drewsum/audio_visualiser/hdw/project_lib/3d_models/Abracon_ASE_3.2x2.5mm.step

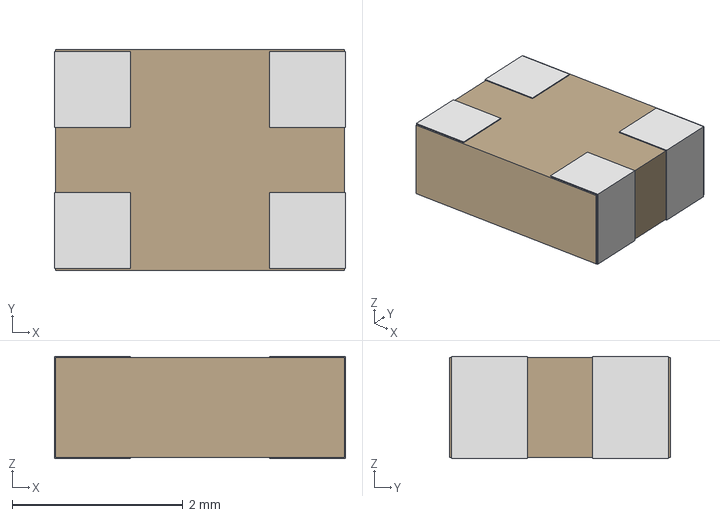
[picture p20: CAD file, 2026-10-09]
hdw/project_lib/3d_models/Abracon_ASE_3.2x2.5mm.step
3.40 x 2.59 x 1.19 mm
