drewsum/audio_visualiser/hdw/project_lib/3d_models/TI_TPS259474_RPW0010A.step

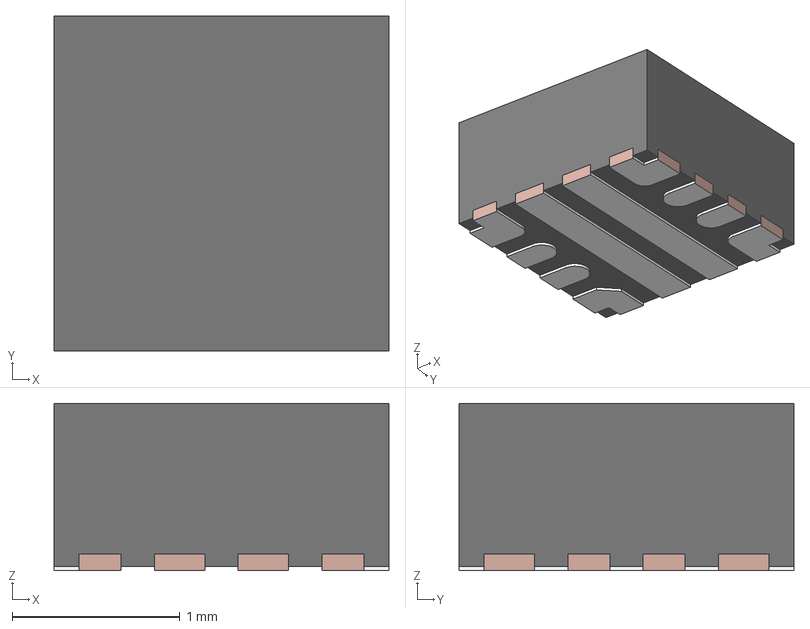
[picture p21: CAD file, 2026-10-09]
hdw/project_lib/3d_models/TI_TPS259474_RPW0010A.step
2.00 x 2.00 x 1.00 mm
FRAME
MOLD
