drewsum/audio_visualiser/hdw/project_lib/3d_models/JAE_DX07S016JA1R1500.step

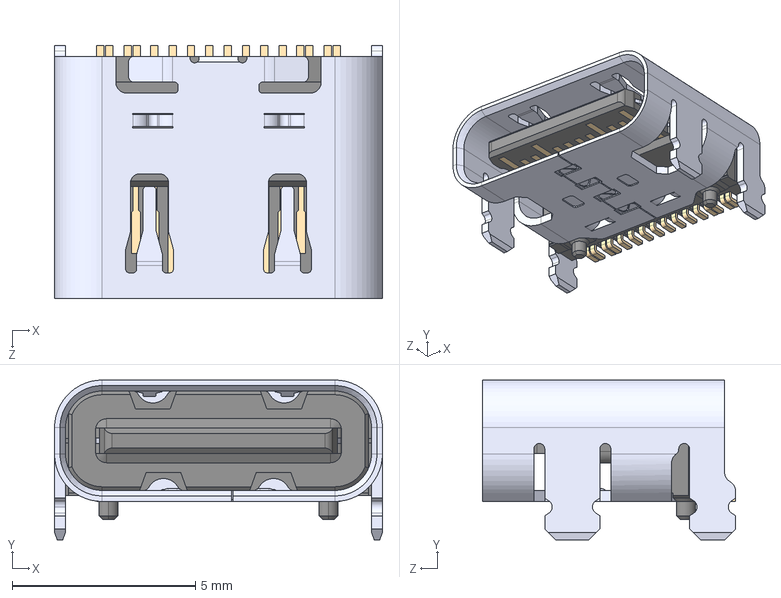
[picture p22: CAD file, 2026-10-09]
hdw/project_lib/3d_models/JAE_DX07S016JA1R1500.step
8.94 x 4.36 x 6.90 mm
