drewsum/audio_visualiser/hdw/project_lib/3d_models/Qorvo_TQFN66-48-1EP_6x6mm_P0.4mm_EP4.2x4.2mm.step

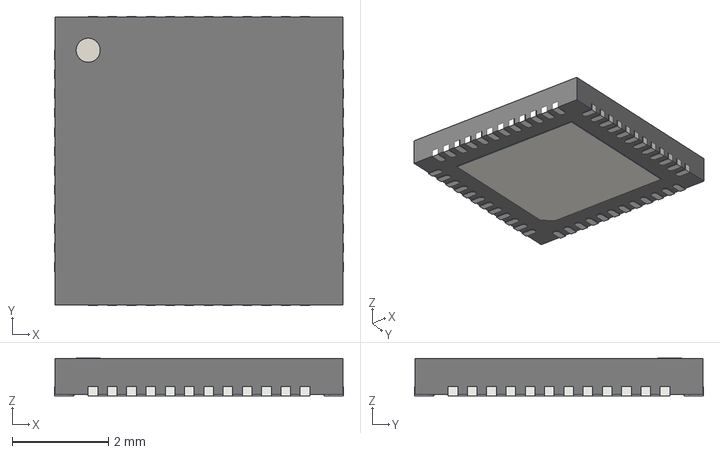
[picture p23: CAD file, 2026-10-09]
hdw/project_lib/3d_models/Qorvo_TQFN66-48-1EP_6x6mm_P0.4mm_EP4.2x4.2mm.step
6.00 x 6.00 x 0.785 mm
