drewsum/audio_visualiser/hdw/project_lib/3d_models/R_0402_1005Metric.step

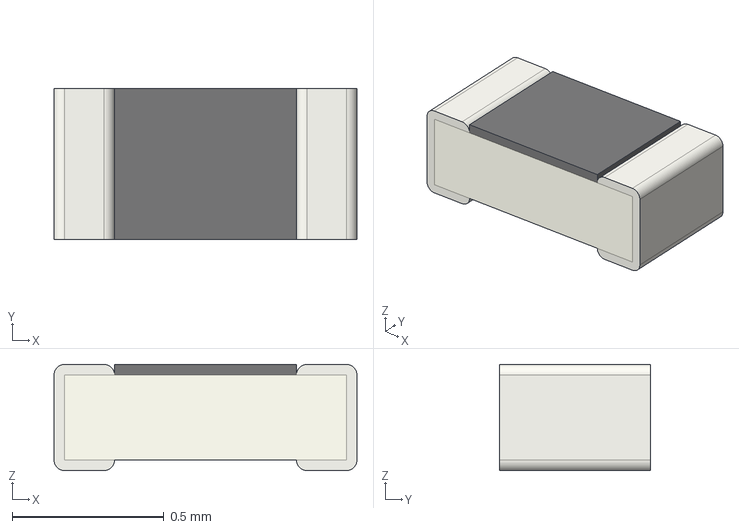
[picture p24: CAD file, 2026-10-09]
hdw/project_lib/3d_models/R_0402_1005Metric.step
1.00 x 0.5 x 0.35 mm
