drewsum/audio_visualiser/hdw/project_lib/3d_models/L_Vishay_IHLP-1212.step

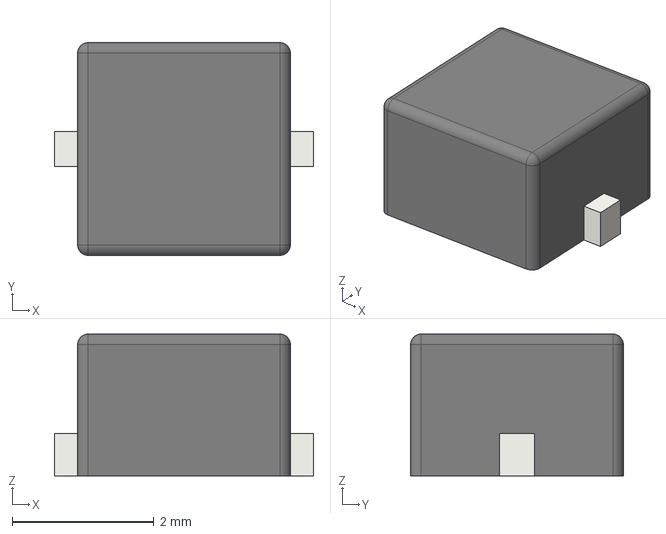
[picture p25: CAD file, 2026-10-09]
hdw/project_lib/3d_models/L_Vishay_IHLP-1212.step
3.65 x 3.00 x 2.00 mm
