drewsum/audio_visualiser/hdw/project_lib/3d_models/IDC-Header_2x15_P2.54mm_Vertical.step

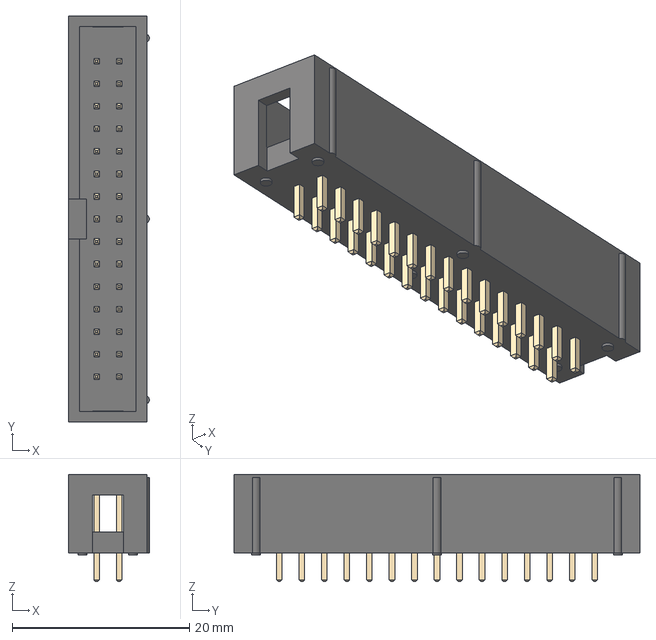
[picture p26: CAD file, 2026-10-09]
hdw/project_lib/3d_models/IDC-Header_2x15_P2.54mm_Vertical.step
9.10 x 45.8 x 12.1 mm
