drewsum/audio_visualiser/hdw/project_lib/3d_models/SW_PUSH_6mm.step

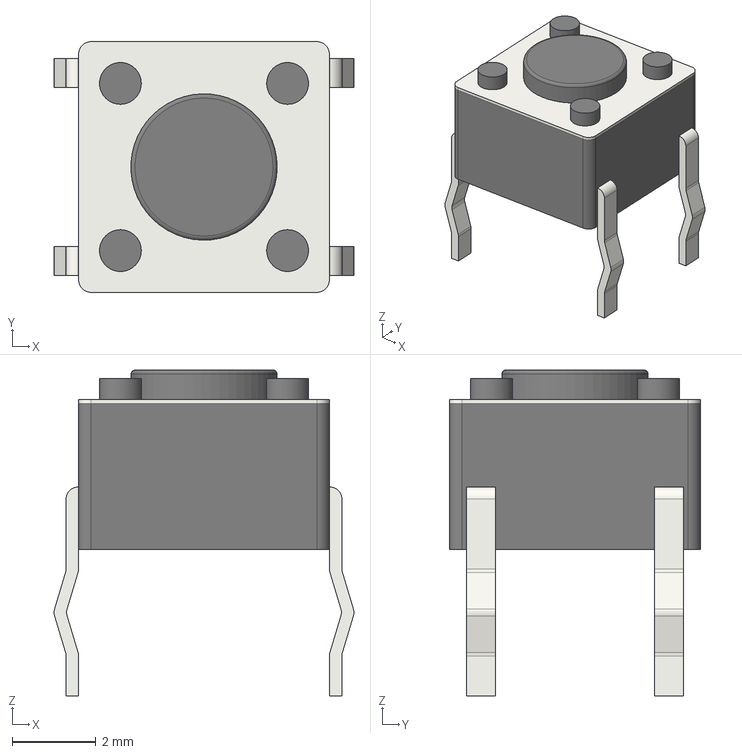
[picture p29: CAD file, 2026-10-09]
hdw/project_lib/3d_models/SW_PUSH_6mm.step
7.17 x 6.00 x 7.80 mm
