drewsum/audio_visualiser/hdw/project_lib/3d_models/CP_EIA-7343-43_Kemet-X.step

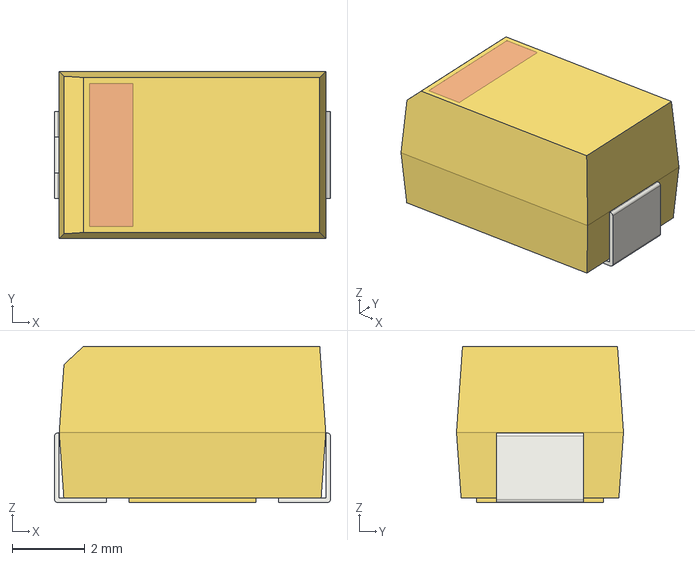
[picture p31: CAD file, 2026-10-09]
hdw/project_lib/3d_models/CP_EIA-7343-43_Kemet-X.step
7.60 x 4.60 x 4.30 mm
