drewsum/audio_visualiser/hdw/project_lib/3d_models/DFN-8-1EP_3x2mm_P0.5mm_EP1.3x1.5mm.step

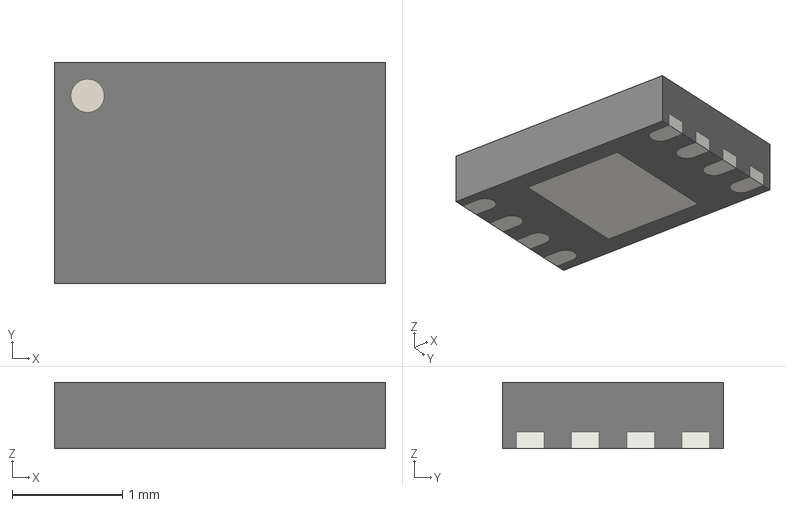
[picture p32: CAD file, 2026-10-09]
hdw/project_lib/3d_models/DFN-8-1EP_3x2mm_P0.5mm_EP1.3x1.5mm.step
3.00 x 2.00 x 0.6 mm
