drewsum/audio_visualiser/hdw/project_lib/3d_models/Texas_S-PVSON-N10.step

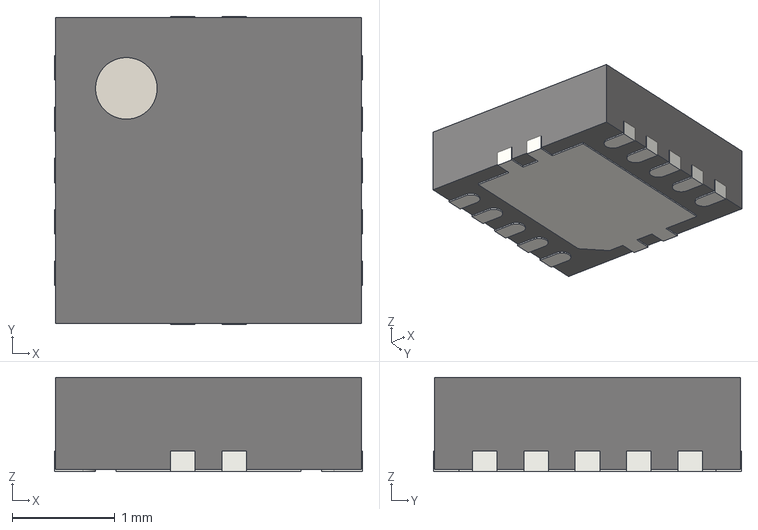
[picture p34: CAD file, 2026-10-09]
hdw/project_lib/3d_models/Texas_S-PVSON-N10.step
3.00 x 3.00 x 0.92 mm
