drewsum/audio_visualiser/hdw/project_lib/3d_models/SOT-363_SC-70-6.step

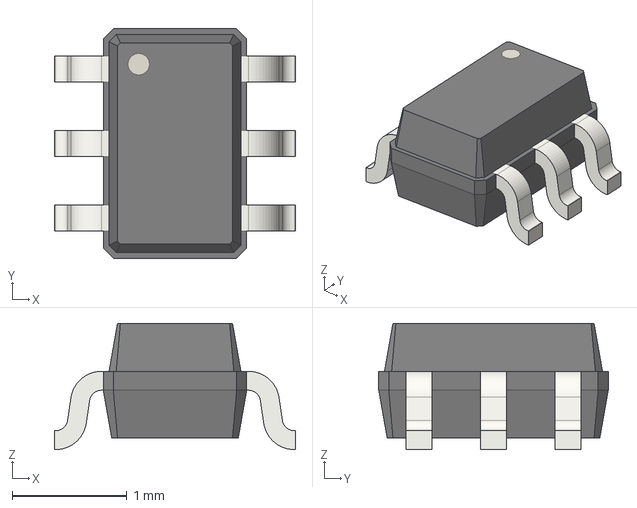
[picture p35: CAD file, 2026-10-09]
hdw/project_lib/3d_models/SOT-363_SC-70-6.step
2.10 x 2.00 x 1.10 mm
