drewsum/audio_visualiser/hdw/project_lib/3d_models/L_Wuerth_PMCI-252012.step

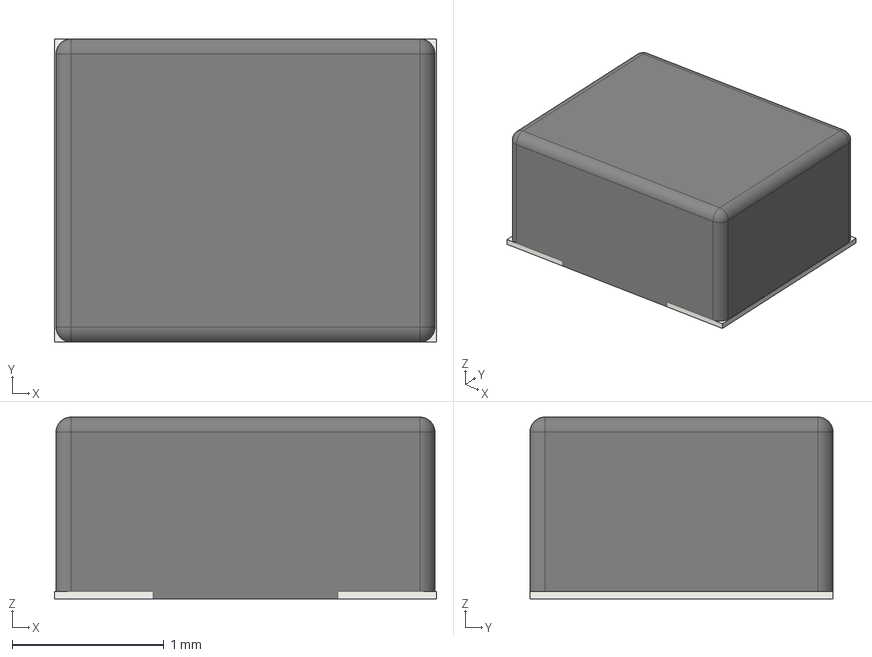
[picture p37: CAD file, 2026-10-09]
hdw/project_lib/3d_models/L_Wuerth_PMCI-252012.step
2.52 x 2.00 x 1.20 mm
