drewsum/audio_visualiser/hdw/project_lib/3d_models/PinHeader_1x01_P2.54mm_Horizontal.step

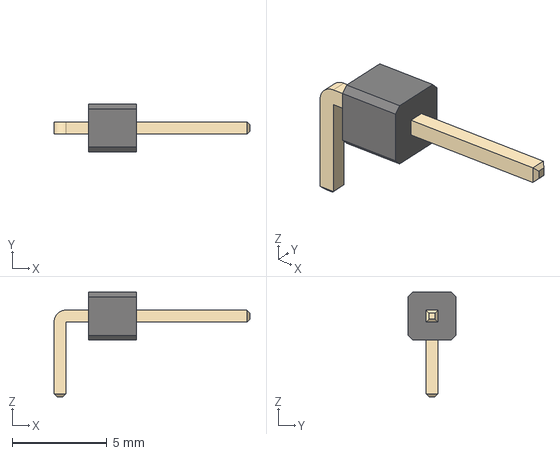
[picture p38: CAD file, 2026-10-09]
hdw/project_lib/3d_models/PinHeader_1x01_P2.54mm_Horizontal.step
10.4 x 2.54 x 5.54 mm
