drewsum/audio_visualiser/hdw/project_lib/3d_models/D_SMA.step

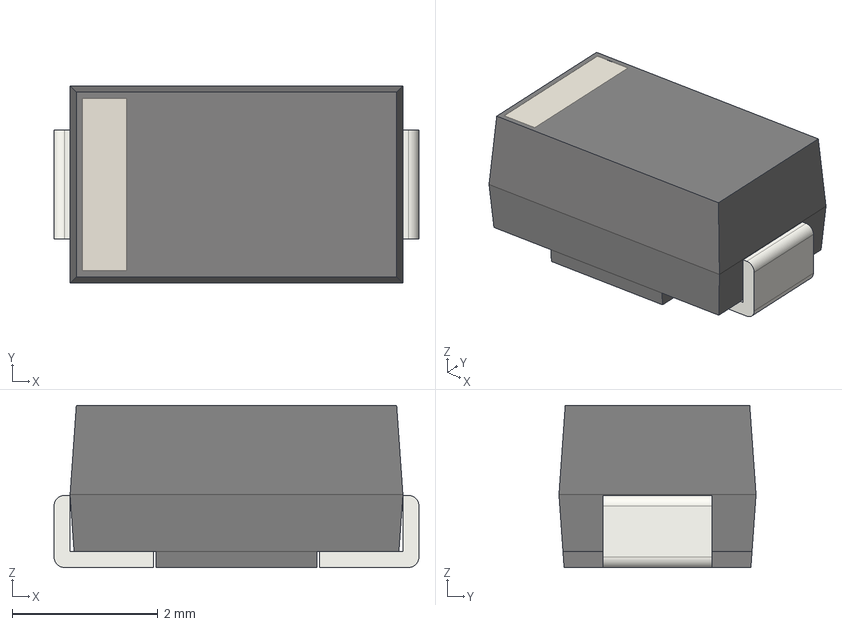
[picture p39: CAD file, 2026-10-09]
hdw/project_lib/3d_models/D_SMA.step
5.00 x 2.70 x 2.22 mm
