drewsum/audio_visualiser/hdw/project_lib/3d_models/VSSOP-8_3x3mm_P0.65mm.step

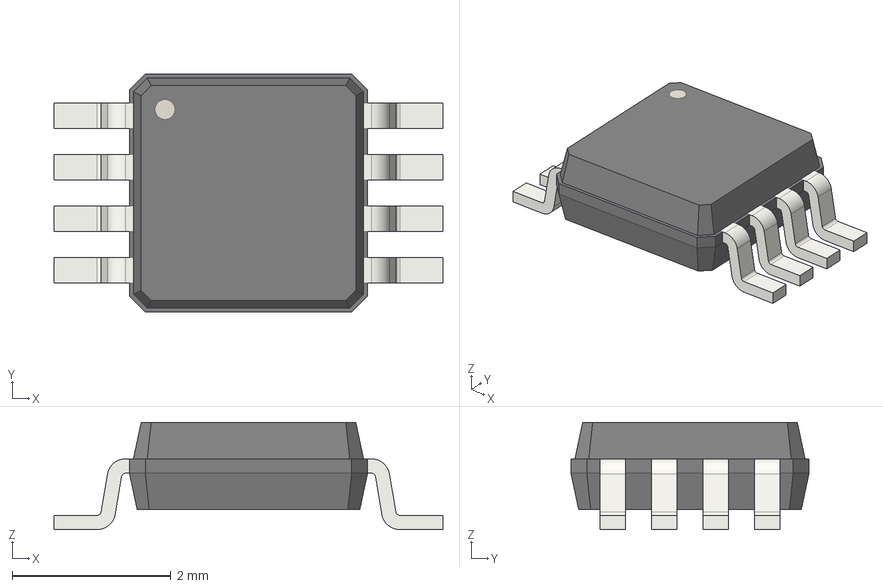
[picture p40: CAD file, 2026-10-09]
hdw/project_lib/3d_models/VSSOP-8_3x3mm_P0.65mm.step
4.90 x 3.00 x 1.35 mm
