drewsum/audio_visualiser/hdw/project_lib/3d_models/TSSOP-14_4.4x5mm_P0.65mm.step

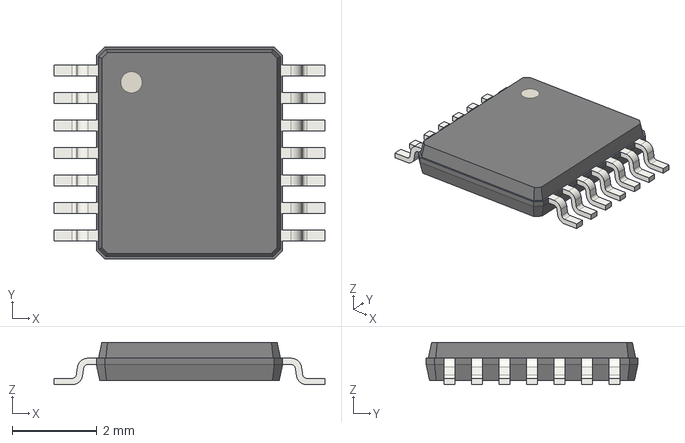
[picture p41: CAD file, 2026-10-09]
hdw/project_lib/3d_models/TSSOP-14_4.4x5mm_P0.65mm.step
6.40 x 5.00 x 1.00 mm
