drewsum/audio_visualiser/hdw/project_lib/3d_models/VSSOP-8_2.3x2mm_P0.5mm.step

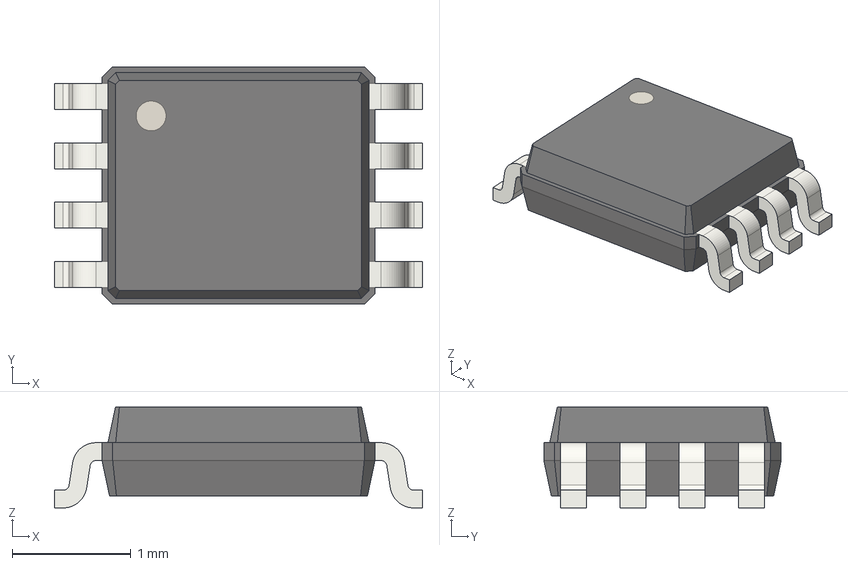
[picture p42: CAD file, 2026-10-09]
hdw/project_lib/3d_models/VSSOP-8_2.3x2mm_P0.5mm.step
3.10 x 2.00 x 0.85 mm
