drewsum/audio_visualiser/hdw/project_lib/3d_models/D_SOD-323.step

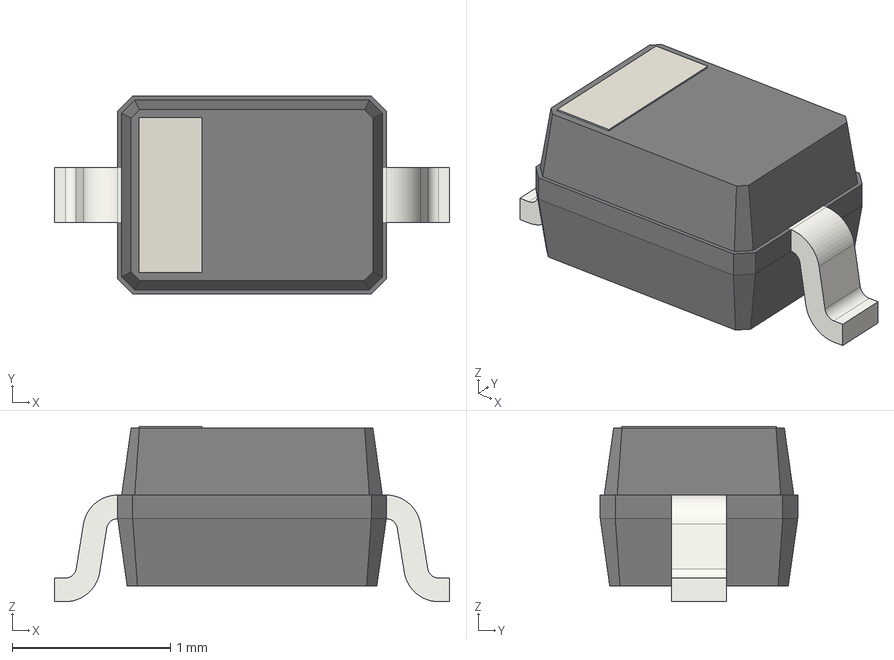
[picture p43: CAD file, 2026-10-09]
hdw/project_lib/3d_models/D_SOD-323.step
2.50 x 1.25 x 1.11 mm
