drewsum/audio_visualiser/hdw/project_lib/3d_models/PinSocket_1x07_P2.54mm_Vertical.step

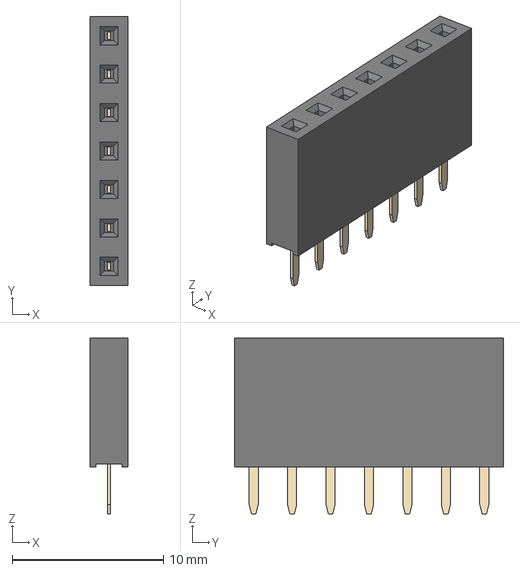
[picture p44: CAD file, 2026-10-09]
hdw/project_lib/3d_models/PinSocket_1x07_P2.54mm_Vertical.step
2.54 x 17.8 x 11.6 mm
