drewsum/audio_visualiser/hdw/project_lib/3d_models/Texas_DSBGA-12_1.36x1.86mm_Layout3x4_P0.5mm.step

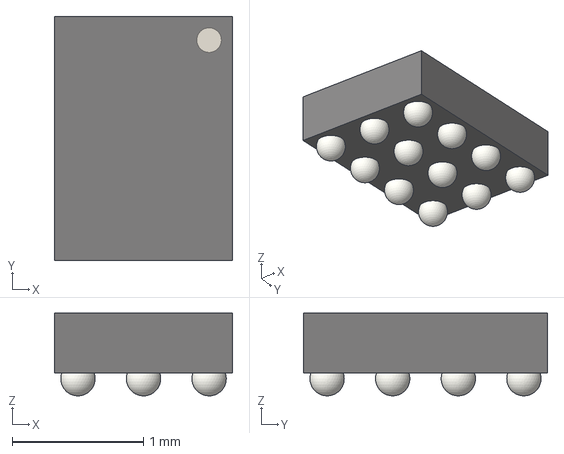
[picture p45: CAD file, 2026-10-09]
hdw/project_lib/3d_models/Texas_DSBGA-12_1.36x1.86mm_Layout3x4_P0.5mm.step
1.36 x 1.86 x 0.631 mm
