drewsum/audio_visualiser/hdw/project_lib/3d_models/R_Array_Convex_8x0602.step

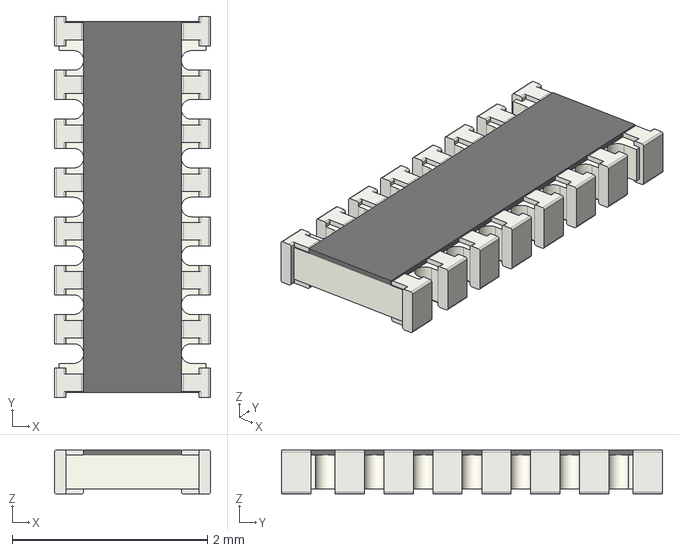
[picture p46: CAD file, 2026-10-09]
hdw/project_lib/3d_models/R_Array_Convex_8x0602.step
1.60 x 3.90 x 0.45 mm
