drewsum/audio_visualiser/hdw/project_lib/3d_models/PinSocket_1x06_P2.54mm_Vertical.step

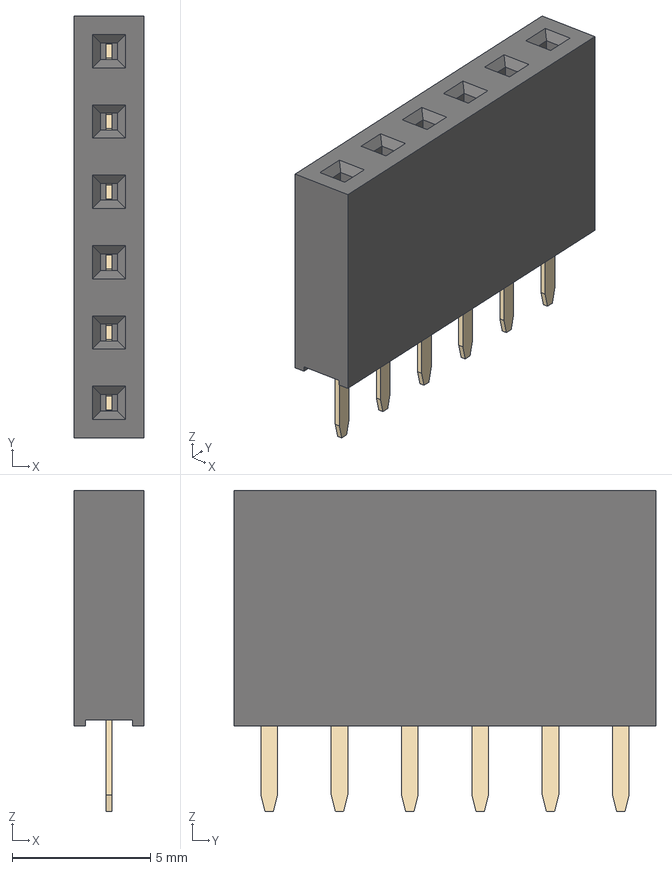
[picture p47: CAD file, 2026-10-09]
hdw/project_lib/3d_models/PinSocket_1x06_P2.54mm_Vertical.step
2.54 x 15.2 x 11.6 mm
