drewsum/audio_visualiser/hdw/project_lib/3d_models/SOT-23-6.step

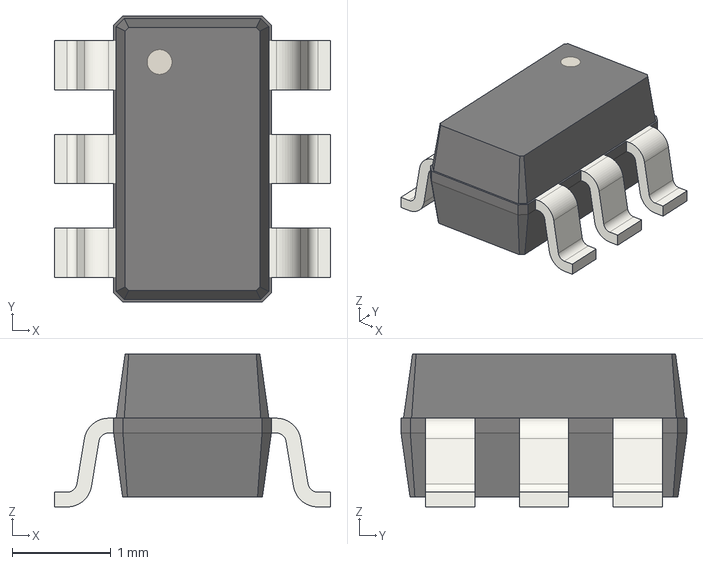
[picture p48: CAD file, 2026-10-09]
hdw/project_lib/3d_models/SOT-23-6.step
2.80 x 2.90 x 1.55 mm
