drewsum/audio_visualiser/hdw/project_lib/3d_models/PinSocket_1x03_P2.54mm_Vertical.step

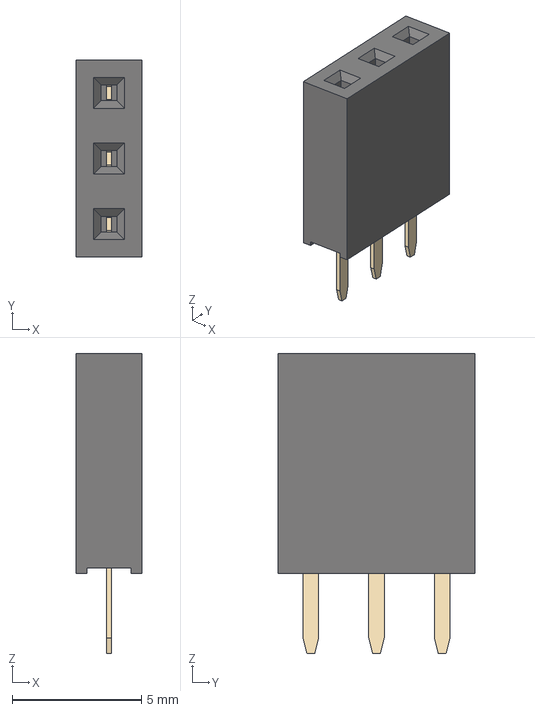
[picture p49: CAD file, 2026-10-09]
hdw/project_lib/3d_models/PinSocket_1x03_P2.54mm_Vertical.step
2.54 x 7.62 x 11.6 mm
